cxdzyq1110/NPU_on_FPGA/projects/aFPGA/00_user_logic/dcfifo/sync_dual_clock.v

/*-------------------------------------------------------------------------*\
	FILE:			sync_dual_clock.v
	AUTHOR:			Xudong Chen
	CREATED BY:		Xudong Chen
	$Id$
	ABSTRACT:		behavioral code for dual-clock sync module
	
	KEYWORDS:		dual clock, sync
	MODIFICATION HISTORY:
	$Log$
		Xudong 		18/6/20			original version
\*-------------------------------------------------------------------------*/
module sync_dual_clock
#(
parameter	WIDTH = 6,			// 带同步的数据宽度
parameter	SYNC_STAGE = 2		// 同步的级数（级数越多，竞争冒险越少）
)
(
input	wire				clock_dst,
input	wire	[WIDTH-1:0]	src,
output	wire	[WIDTH-1:0]	dst
);

//
reg		[WIDTH-1:0]			sync_reg	[0:SYNC_STAGE-1];
integer p;
always @(posedge clock_dst)
begin
	sync_reg[0] <= src;
	for(p=1; p<SYNC_STAGE; p=p+1)
		sync_reg[p] <= sync_reg[p-1];
end

assign						dst = sync_reg[SYNC_STAGE-1];	// 输出

endmodule
