cxdzyq1110/NPU_on_FPGA/projects/aFPGA/00_user_logic/npu/npu_inst_join.v

module npu_inst_join
(
	input	wire			npu_inst_clk, npu_inst_rst_n,
	input	wire	[31:0]	npu_inst_part,
	input	wire			npu_inst_part_en,
	output	reg		[127:0]	npu_inst,
	output	reg				npu_inst_en
);

	wire	RESETN = npu_inst_rst_n;
	// 生成npu_inst/npu_inst_en
	// 要用状态机来生成
	reg		[3:0]	npu_inst_state;
	reg		[31:0]	npu_inst_delay;	// 延时计数单元，如果超时了，就说明指令传输完成
	always @(posedge npu_inst_clk)
		if(!RESETN)
		begin
			npu_inst_state <= 0;
			npu_inst <= 0;
			npu_inst_en <= 0;
			npu_inst_delay <= 0;
		end
		else
		begin
			case(npu_inst_state)
				0: begin
					if(npu_inst_part_en)
					begin
						npu_inst <= {npu_inst[95:0], npu_inst_part};
						npu_inst_en <= 0;
						npu_inst_state <= 1;
						npu_inst_delay <= 0;
					end
				end
				
				// 等待超时了，就说明指令传输完成
				1: begin
					if(npu_inst_part_en)
					begin
						npu_inst <= {npu_inst[95:0], npu_inst_part};
						npu_inst_en <= 0;
						npu_inst_delay <= 0;
					end
					else if(npu_inst_delay>=2000000)	// 40ms超时等待机制
					begin
						npu_inst_en <= 1;
						npu_inst_state <= 2;
						npu_inst_delay <= 0;
					end
					else 
						npu_inst_delay <= npu_inst_delay + 1;	// 超时等待计数器++
				end
				
				// 
				2: begin
					npu_inst_en <= 0;
					npu_inst_state <= 0;
				end
				
				default: begin
					npu_inst_state <= 0;
					npu_inst <= 0;
					npu_inst_en <= 0;
					npu_inst_delay <= 0;
				end
				
			endcase
		end
		
endmodule
